YoannLe/Frigo-Ctl/Nextion/Images/Sources/160_F_170761153_mHWMTj9BhgyiKmSzQbuPNP8HVWtOIVWv.jpg

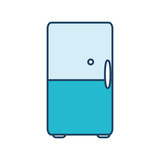
Nextion/Images/Sources/160_F_170761153_mHWMTj9BhgyiKmSzQbuPNP8HVWtOIVWv.jpg
