YoannLe/Frigo-Ctl/Nextion/Images/Sources/RPM_Gauge-125.png

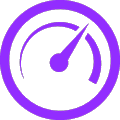
Nextion/Images/Sources/RPM_Gauge-125.png
