YoannLe/Frigo-Ctl/PCB/Frigo-Ctl/PCB.png

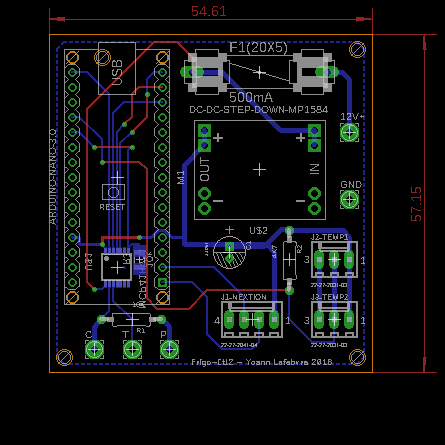
PCB/Frigo-Ctl/PCB.png
