YoannLe/Frigo-Ctl/Photos/IMG_20180602_082727.jpg

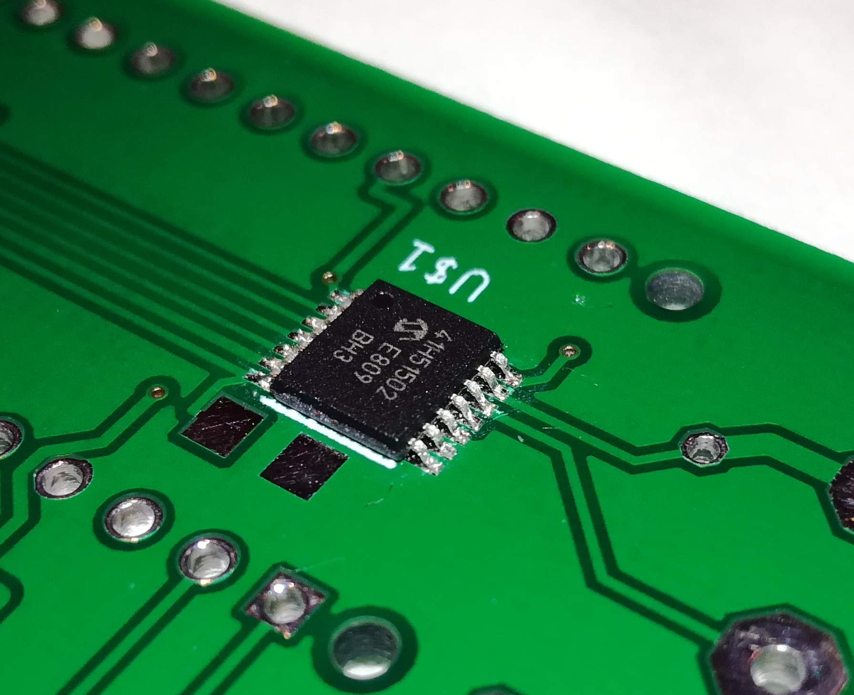
Photos/IMG_20180602_082727.jpg
