YoannLe/Frigo-Ctl/Photos/IMG_20180602_082736.jpg

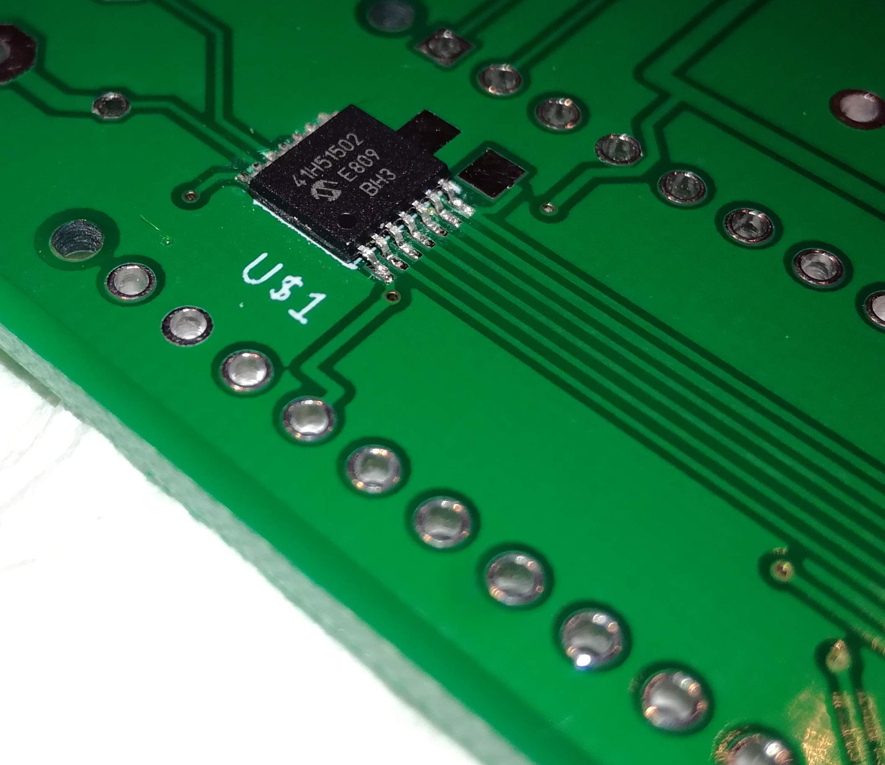
Photos/IMG_20180602_082736.jpg
