YoannLe/Frigo-Ctl/Photos/IMG_20180602_103338.jpg

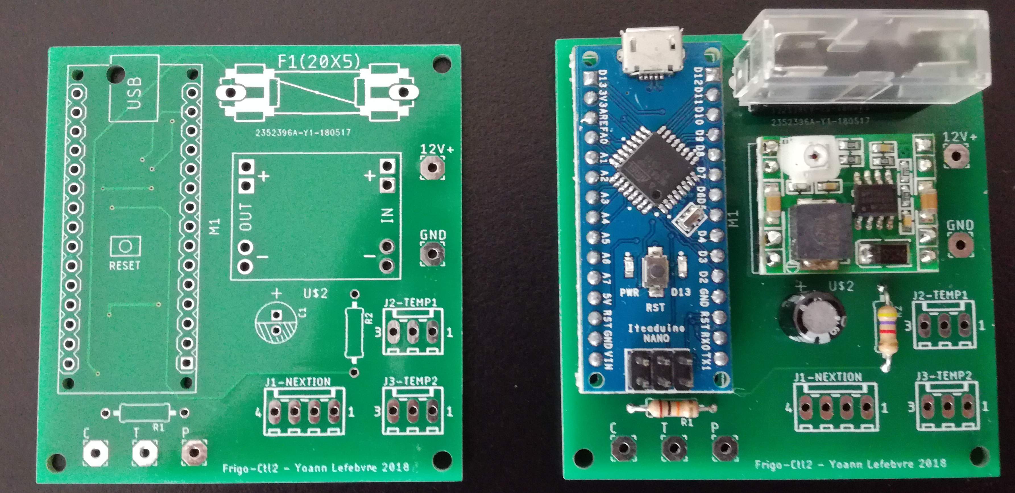
Photos/IMG_20180602_103338.jpg
