YoannLe/Frigo-Ctl/Photos/IMG_20180602_103403.jpg

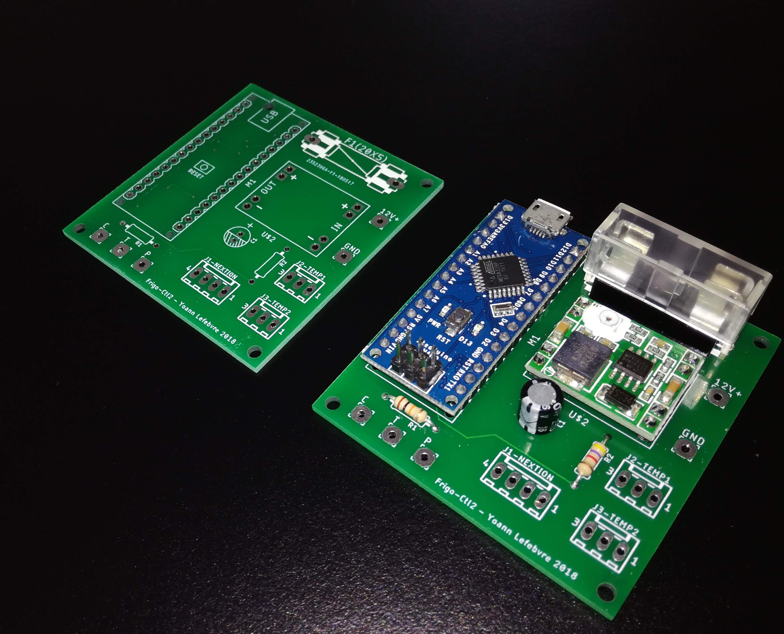
Photos/IMG_20180602_103403.jpg
