YoannLe/Frigo-Ctl/Photos/IMG_20180701_204629.jpg

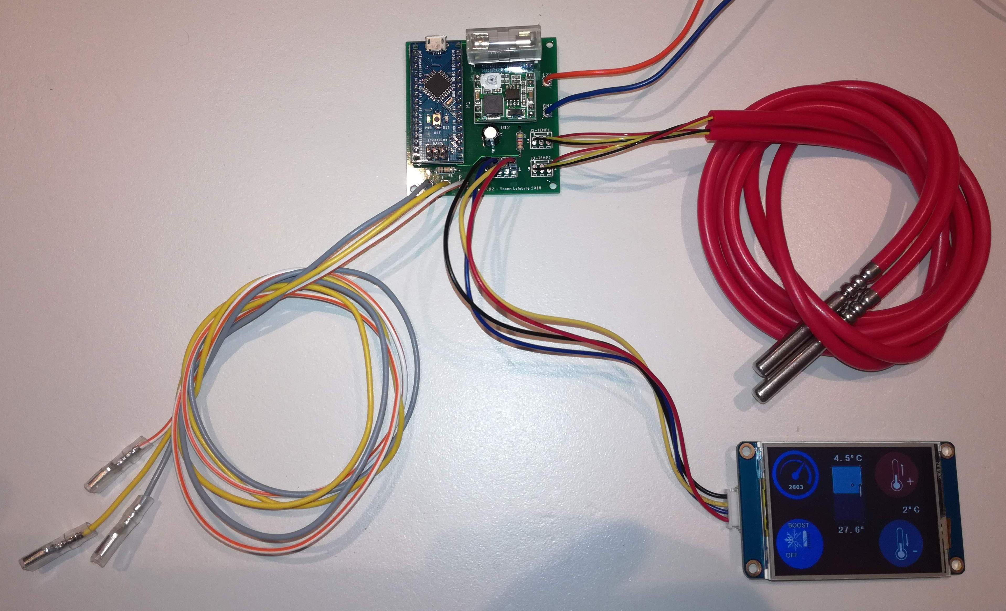
Photos/IMG_20180701_204629.jpg
