YoannLe/Frigo-Ctl/Photos/IMG_20180701_204654.jpg

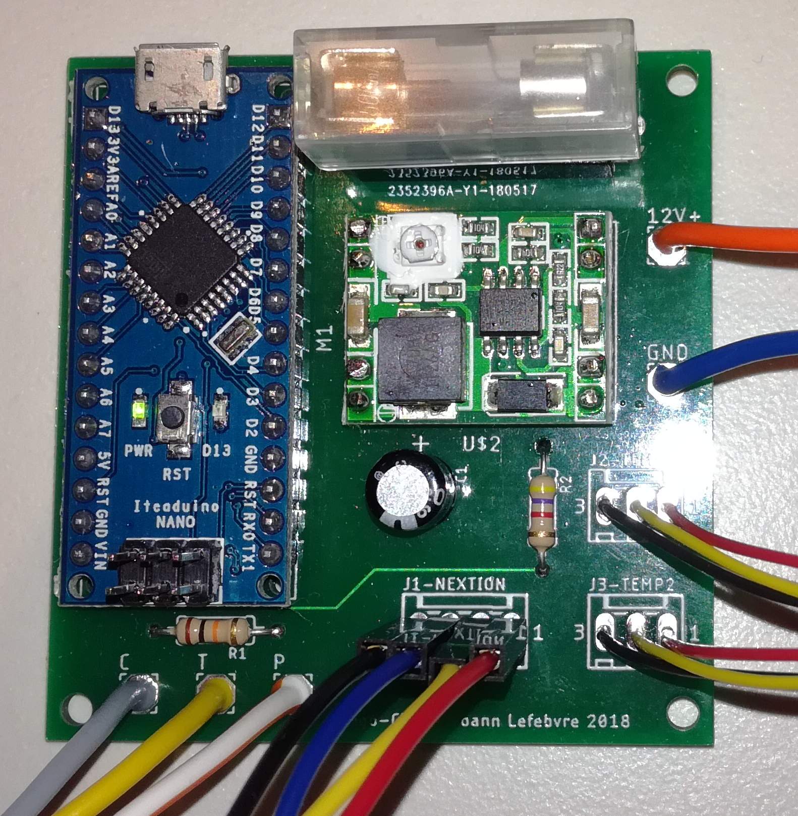
Photos/IMG_20180701_204654.jpg
