YoannLe/Frigo-Ctl/Photos/IMG_20180701_204727.jpg

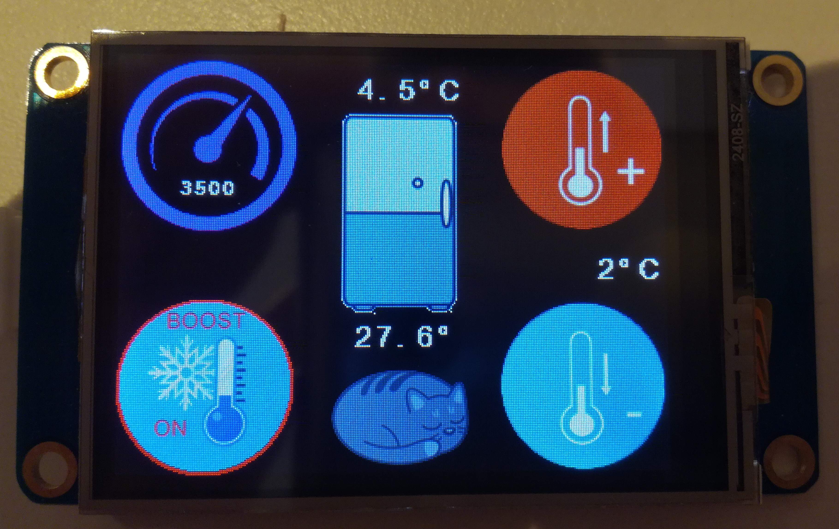
Photos/IMG_20180701_204727.jpg
