YoannLe/Frigo-Ctl/Photos/IMG_20180701_210936.jpg

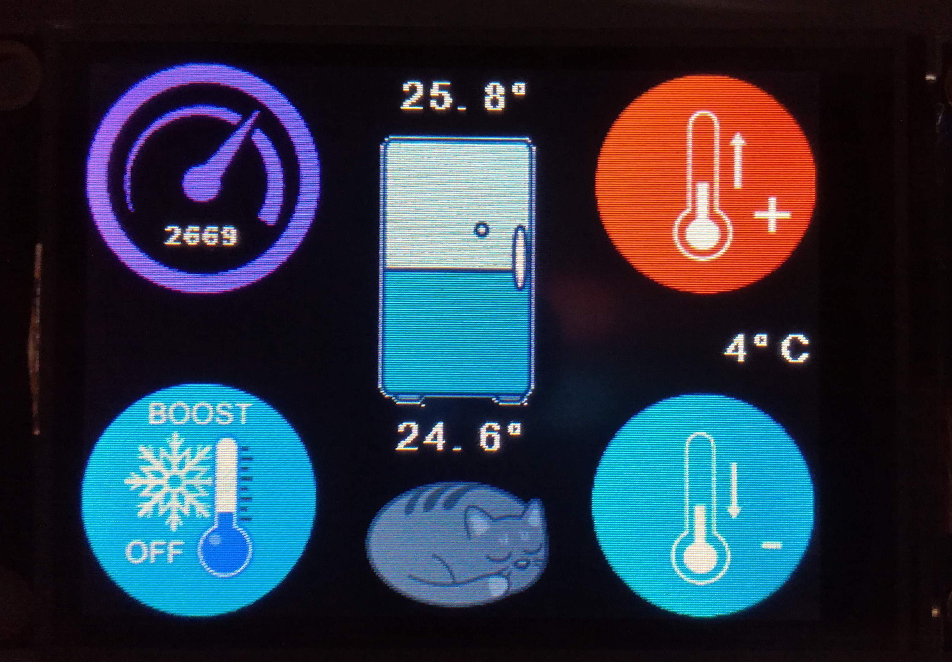
Photos/IMG_20180701_210936.jpg
