YoannLe/Frigo-Ctl/Photos/IMG_20180701_211241.jpg

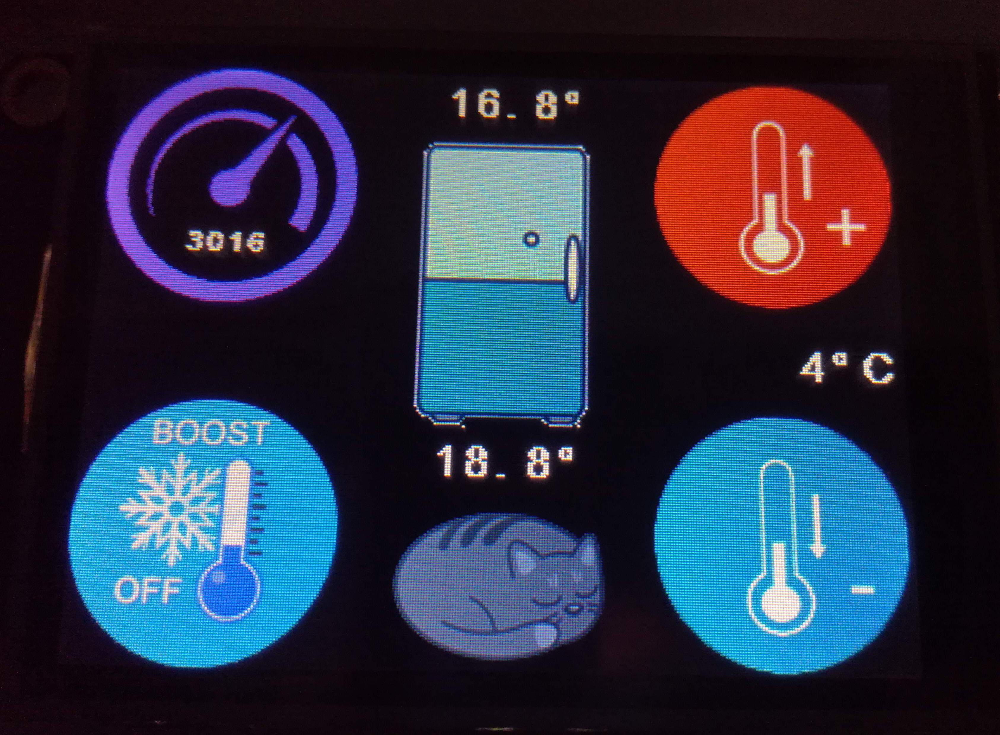
Photos/IMG_20180701_211241.jpg
