YoannLe/Frigo-Ctl/Photos/IMG_20180701_212227_1.jpg

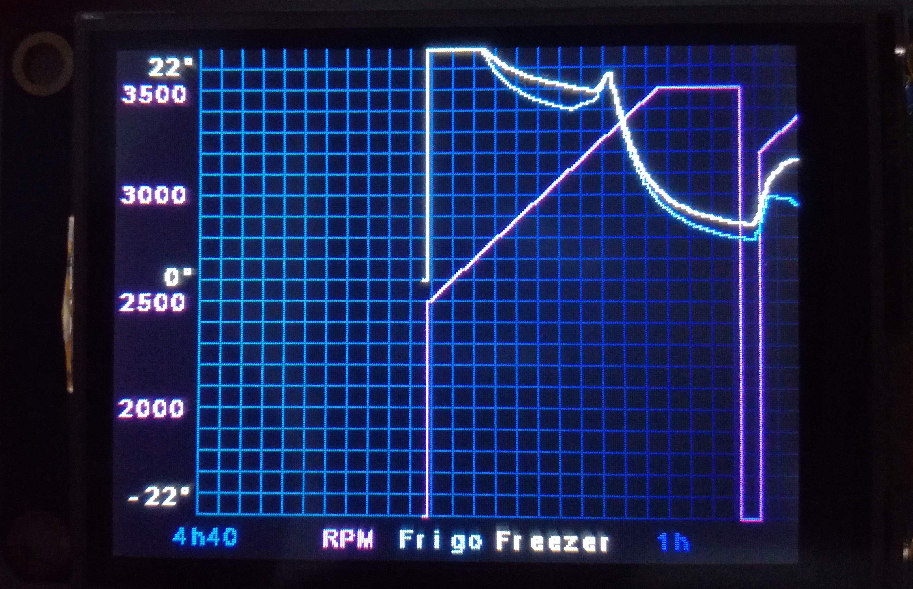
Photos/IMG_20180701_212227_1.jpg
